zampoan/is-plant-okay/ELECTRICAL/is-plant-okay/KICAD_PROJECT_LIBRARY/UJ20_C_H_G_SMT_5_P16_TR/UJ20-C-H-G-SMT-5-P16-TR.step

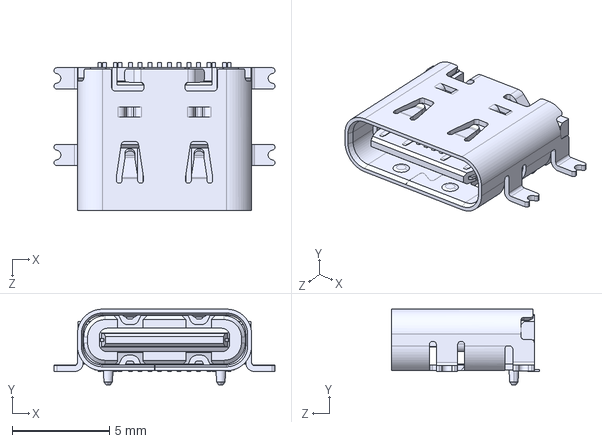
[picture p16: CAD file, 2025-12-18]
ELECTRICAL/is-plant-okay/KICAD_PROJECT_LIBRARY/UJ20_C_H_G_SMT_5_P16_TR/UJ20-C-H-G-SMT-5-P16-TR.step
11.3 x 3.89 x 7.60 mm
