zampoan/is-plant-okay/ELECTRICAL/is-plant-okay/KICAD_PROJECT_LIBRARY/USB4085_GF_A/USB4085-GF-A.STEP

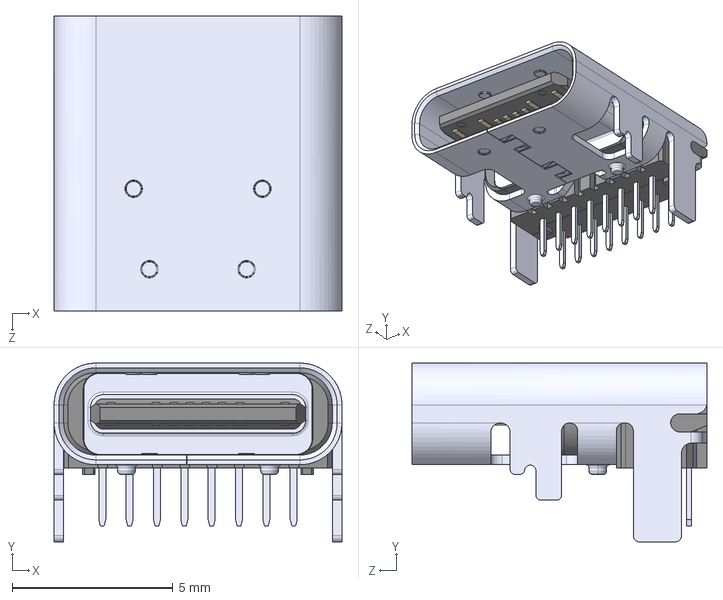
[picture p17: CAD file, 2025-12-15]
ELECTRICAL/is-plant-okay/KICAD_PROJECT_LIBRARY/USB4085_GF_A/USB4085-GF-A.STEP
8.95 x 5.56 x 9.17 mm
