zampoan/is-plant-okay/ELECTRICAL/is-plant-okay/KICAD_PROJECT_LIBRARY/USBLC6_2SC6-2/USBLC6-2SC6.step

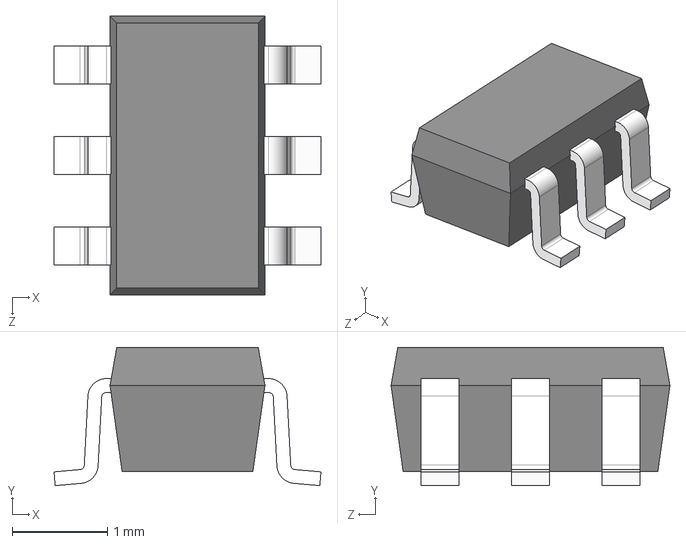
[picture p18: CAD file, 2025-12-15]
ELECTRICAL/is-plant-okay/KICAD_PROJECT_LIBRARY/USBLC6_2SC6-2/USBLC6-2SC6.step
2.80 x 1.45 x 2.92 mm
