zampoan/is-plant-okay/ELECTRICAL/is-plant-okay/KICAD_PROJECT_LIBRARY/Wio-SX1262 Module Kicad Library/Wio-SX1262 file.step

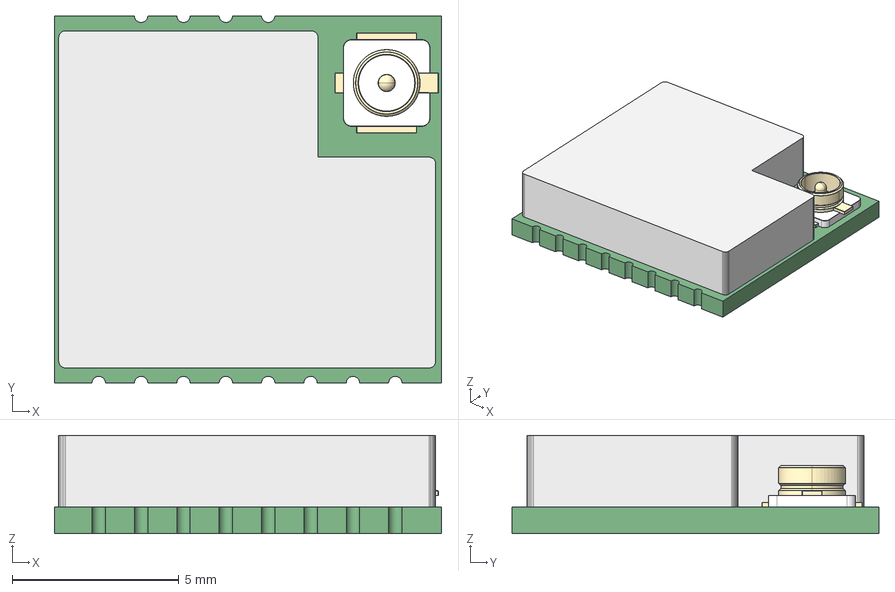
[picture p19: CAD file, 2025-12-15]
ELECTRICAL/is-plant-okay/KICAD_PROJECT_LIBRARY/Wio-SX1262 Module Kicad Library/Wio-SX1262 file.step
11.6 x 11.0 x 2.95 mm
User_Library-IPEX
Extruded
