zampoan/is-plant-okay/ELECTRICAL/is-plant-okay/KICAD_PROJECT_LIBRARY/ZOR_25_B_52_0R/RES_ZOR25_6P3X2P3_YAG.step

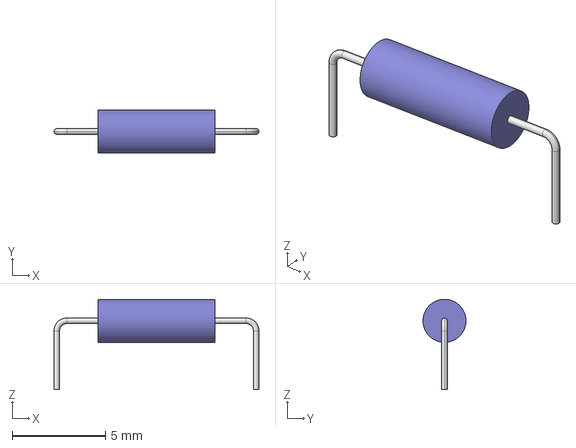
[picture p20: CAD file, 2025-12-18]
ELECTRICAL/is-plant-okay/KICAD_PROJECT_LIBRARY/ZOR_25_B_52_0R/RES_ZOR25_6P3X2P3_YAG.step
11.0 x 2.31 x 4.85 mm
